MOHAMEDELHALOUA/STRF/STRF/finaleProduct/layout3.png

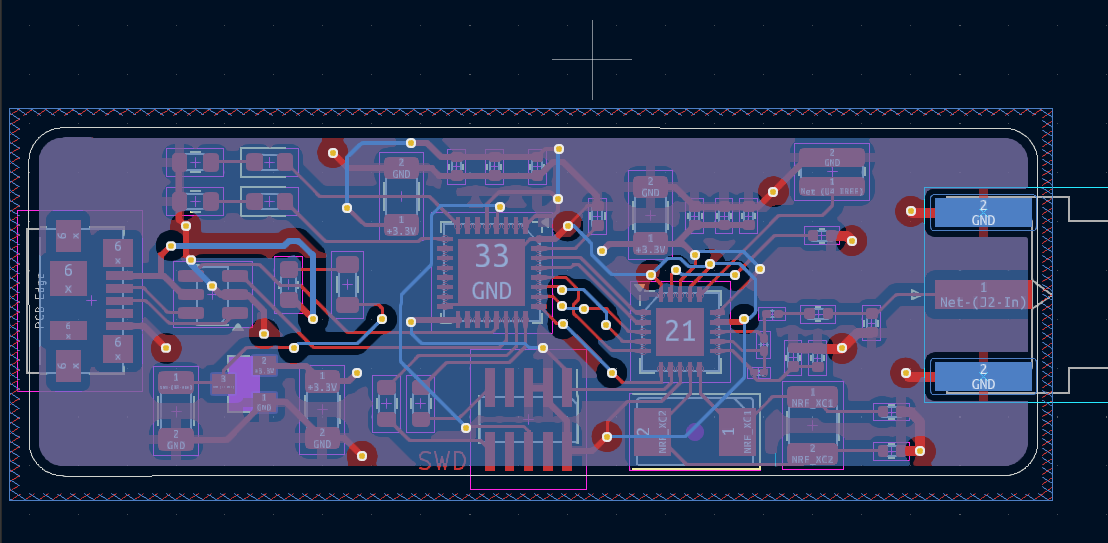
STRF/finaleProduct/layout3.png
